sdalimon/VideoDACRAM/Sim/Video_Out.asc

R1: res; 4k7
R2: res; 12k
R3: res; 1k5
R4: res; 75
R5: res; 75
R6: res; 2k2
R7: res; 2k2
U1: opamp
V1: voltage; PULSE(0 3.3 1m 10n 10n 1m 2m 2)
V2: voltage; PULSE(0 3.3 2m 10n 10n 2m 4m 1)
Named nets: 0, SYNC, VID, OUT
.lib opamp.sub
.tran 5m
